Lachlanric/Robot-Arm-Snatcha/3D/SOLIDWORKS/Assem1.SLDASM

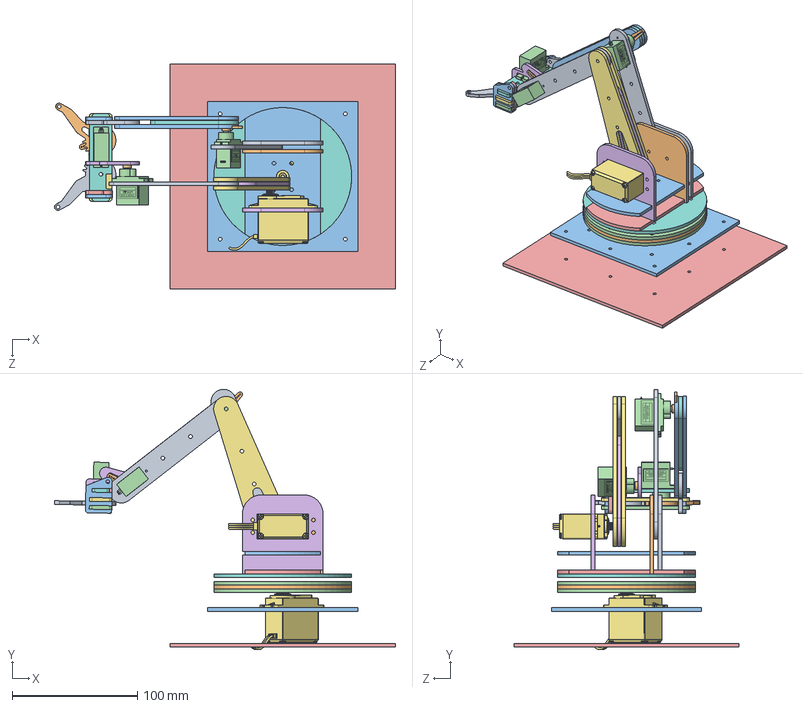
[picture p4: CAD file, 2025-02-07]
3D/SOLIDWORKS/Assem1.SLDASM
272.2 x 207.8 x 180.0 mm
M90S x 3
L1_body x 2
MG90S_horn1 x 3
L1_body - motor mount x 2
L1_body - middle spacing
MG995_large x 2
BaseMotorSlot
BaseHorizontalSlots
CircleBase-InnerBottom
BaseSquare
CircleBase-OuterBottom - 2
BaseMotorSlot_SingleHole
CircleBase-InnerTop - 3
L1_body_taper x 2
L1_body - middle spacing - mg995r taperred
BaseSquare - larger_2
CircleBase - UnderHorn x 2
BaseHorizontalSlots_LastInsert
BaseMotorSlot_SingleHole_LastInsert
Claw_SidePanel
Claw_MotorSlot
Claw_GearSlot
Claw_SidePanel_Short
Claw_SidePanel_Shorter
Claw_Bottom_2
Claw_SidePanel_Shorter - Lock x 2
Gear1
Gear2
