Lachlanric/Robot-Arm-Snatcha/3D/SOLIDWORKS/Claw_SidePanel_Shorter - Lock.SLDPRT

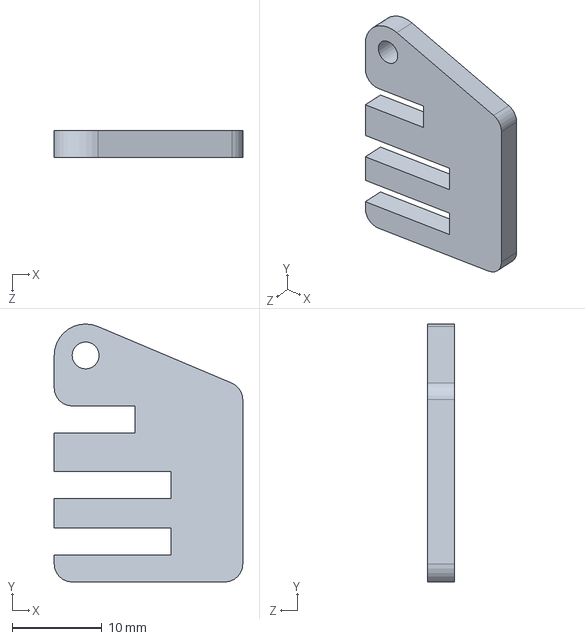
[picture p19: CAD file, 2025-02-05]
3D/SOLIDWORKS/Claw_SidePanel_Shorter - Lock.SLDPRT
21.0 x 28.7 x 3.00 mm
