Lachlanric/Robot-Arm-Snatcha/3D/SOLIDWORKS/BaseSquare - larger_2.SLDPRT

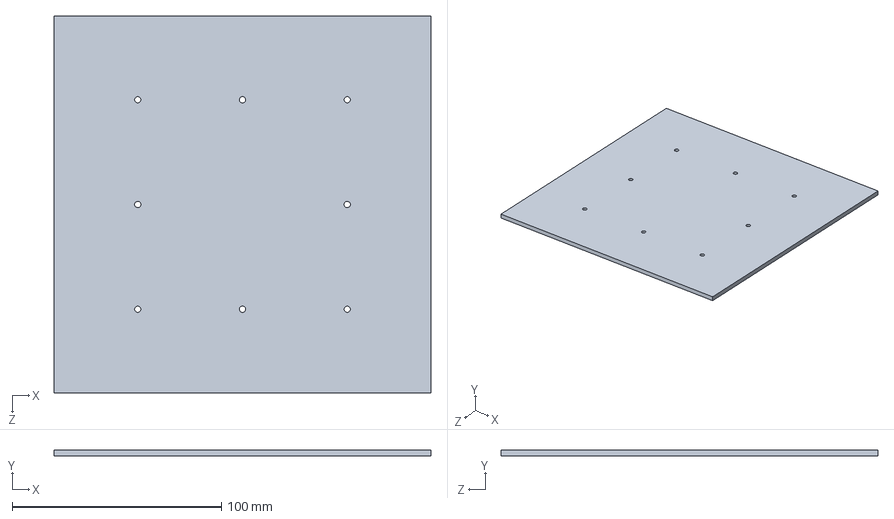
[picture p20: CAD file, 2025-02-05]
3D/SOLIDWORKS/BaseSquare - larger_2.SLDPRT
180.0 x 3.00 x 180.0 mm
