Lachlanric/Robot-Arm-Snatcha/3D/SOLIDWORKS/L1_body_taper.SLDPRT

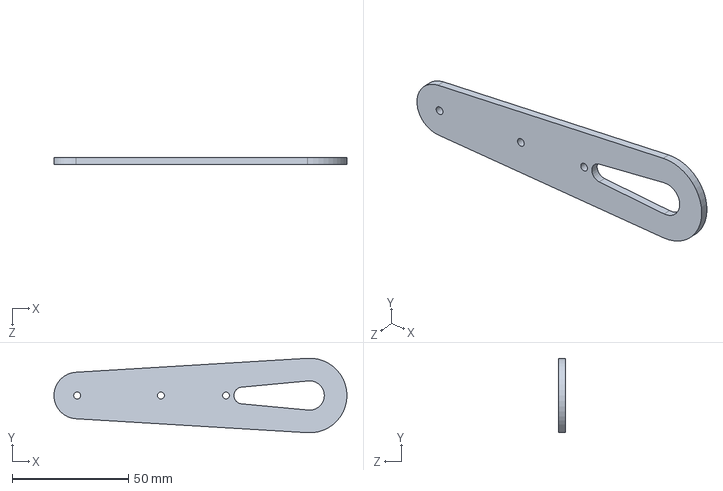
[picture p21: CAD file, 2025-02-05]
3D/SOLIDWORKS/L1_body_taper.SLDPRT
126.0 x 32.0 x 3.00 mm
