Lachlanric/Robot-Arm-Snatcha/3D/SOLIDWORKS/CircleBase-InnerTop - 3.SLDPRT

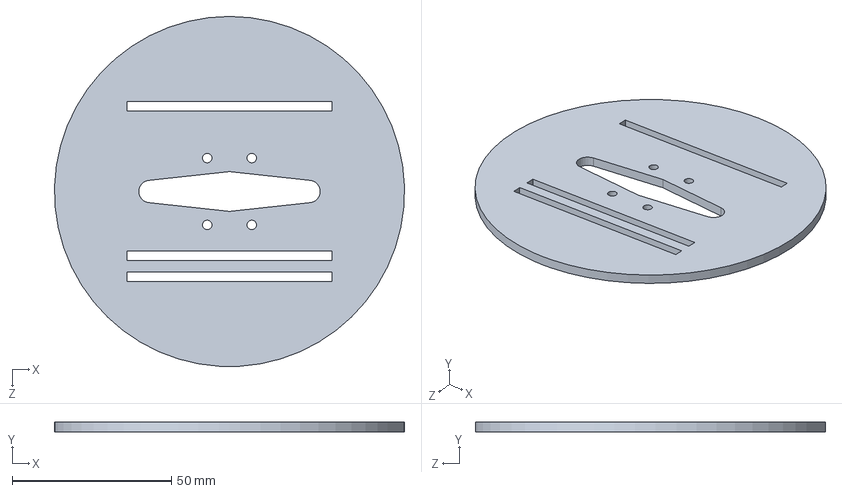
[picture p22: CAD file, 2025-02-05]
3D/SOLIDWORKS/CircleBase-InnerTop - 3.SLDPRT
110.0 x 3.00 x 110.0 mm
