Lachlanric/Robot-Arm-Snatcha/3D/SOLIDWORKS/MG995_large.SLDPRT

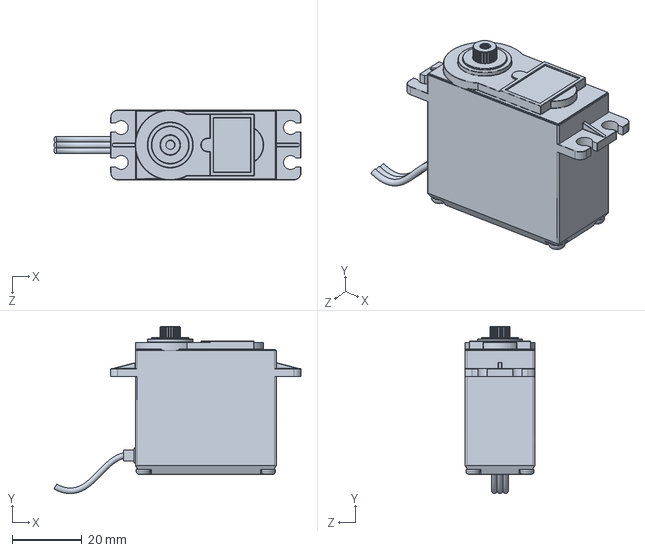
[picture p23: CAD file, 2025-02-05]
3D/SOLIDWORKS/MG995_large.SLDPRT
70.7 x 47.9 x 20.0 mm
