Lachlanric/Robot-Arm-Snatcha/3D/SOLIDWORKS/BaseHorizontalSlots_LastInsert.SLDPRT

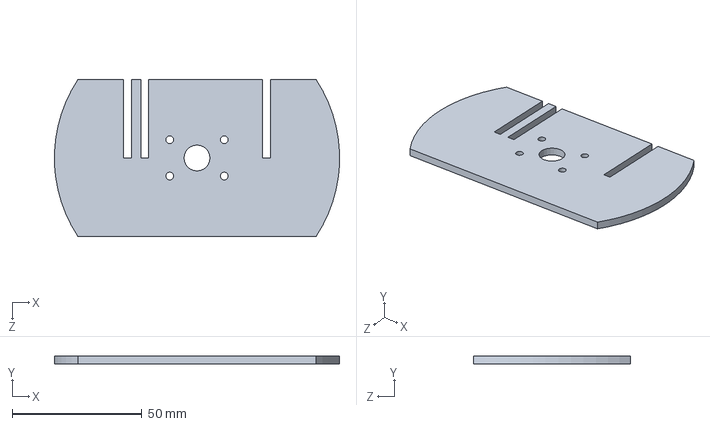
[picture p24: CAD file, 2025-02-05]
3D/SOLIDWORKS/BaseHorizontalSlots_LastInsert.SLDPRT
109.9 x 3.00 x 60.5 mm
