Lachlanric/Robot-Arm-Snatcha/3D/SOLIDWORKS/MG90S_horn1.SLDPRT

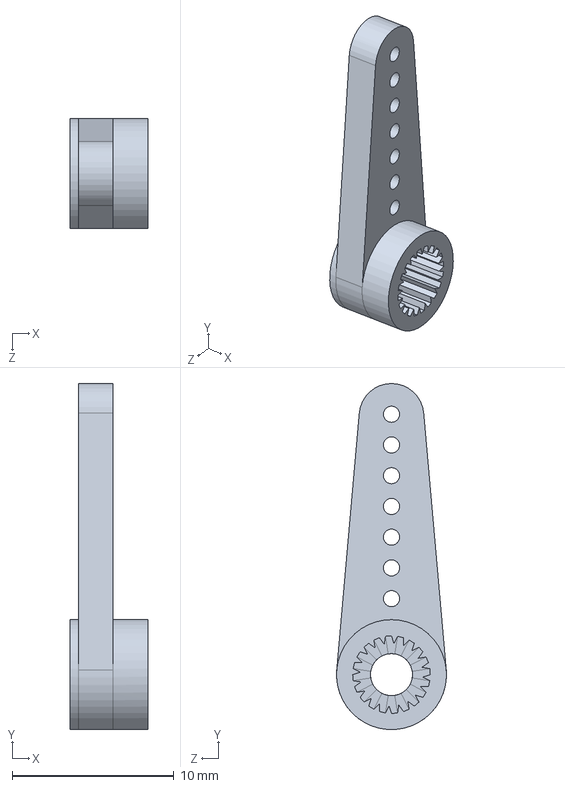
[picture p25: CAD file, 2025-02-05]
3D/SOLIDWORKS/MG90S_horn1.SLDPRT
4.80 x 21.4 x 6.80 mm
