Lachlanric/Robot-Arm-Snatcha/3D/SOLIDWORKS/M90S.SLDPRT

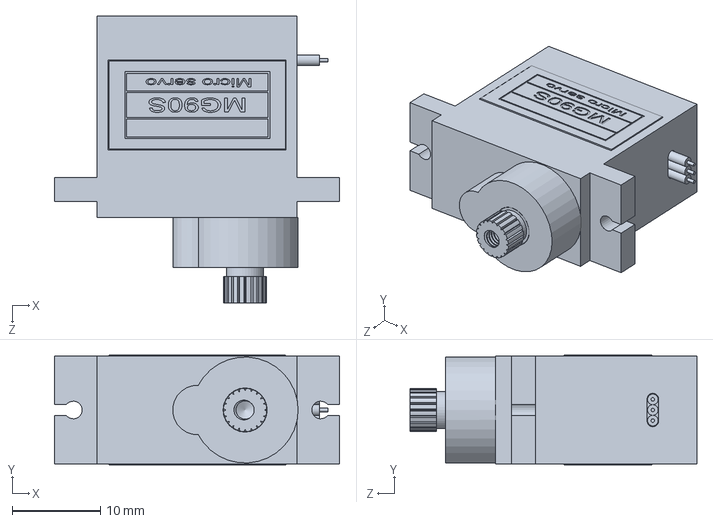
[picture p27: CAD file, 2025-02-05]
3D/SOLIDWORKS/M90S.SLDPRT
32.3 x 12.4 x 32.5 mm
