Lachlanric/Robot-Arm-Snatcha/3D/SOLIDWORKS/BaseMotorSlot_SingleHole_LastInsert.SLDPRT

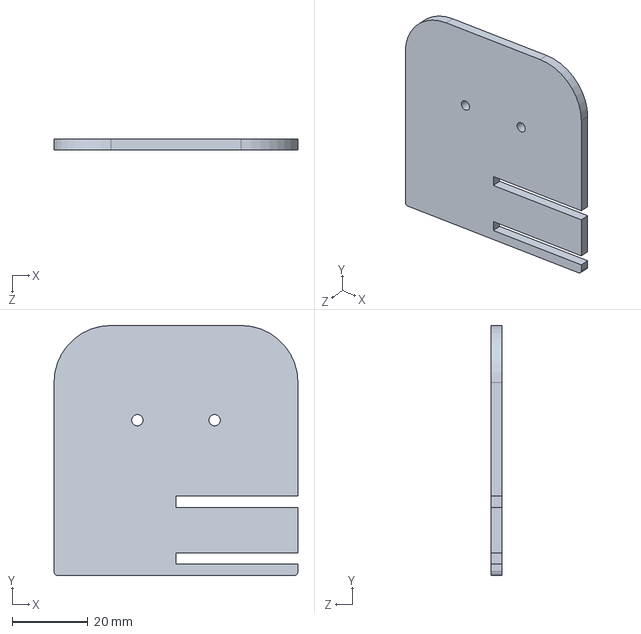
[picture p28: CAD file, 2025-02-05]
3D/SOLIDWORKS/BaseMotorSlot_SingleHole_LastInsert.SLDPRT
64.4 x 66.0 x 3.00 mm
