Lachlanric/Robot-Arm-Snatcha/3D/SOLIDWORKS/L1_body - middle spacing - mg995r taperred.SLDPRT

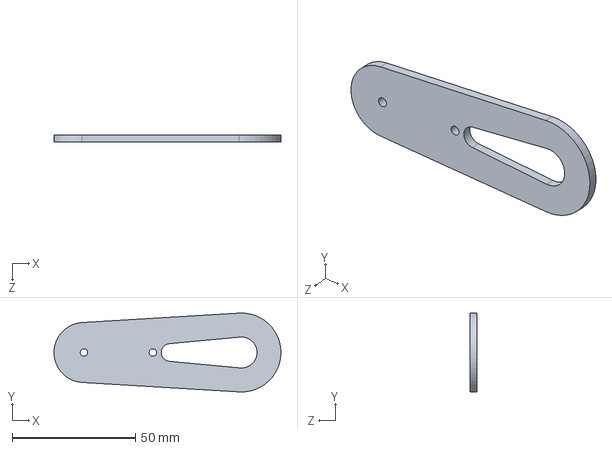
[picture p29: CAD file, 2025-02-05]
3D/SOLIDWORKS/L1_body - middle spacing - mg995r taperred.SLDPRT
92.2 x 32.0 x 3.00 mm
