Lachlanric/Robot-Arm-Snatcha/3D/SOLIDWORKS/L1_body - middle spacing.SLDPRT

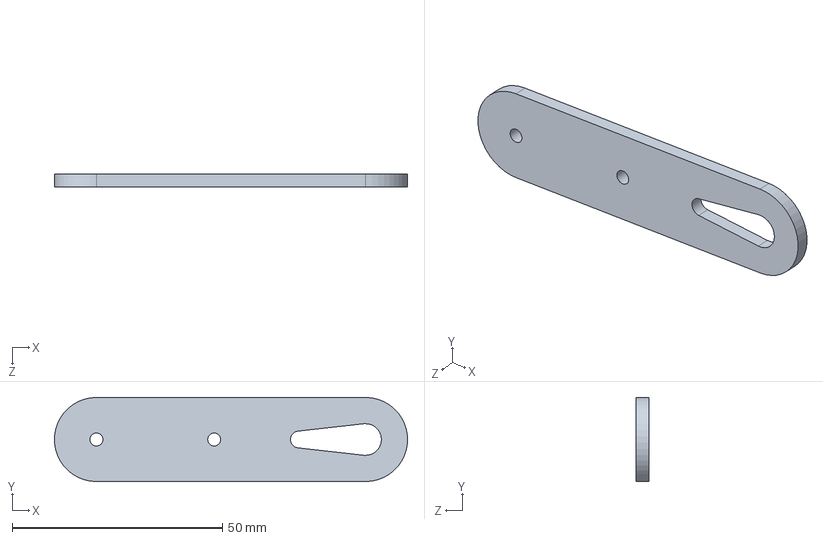
[picture p30: CAD file, 2025-02-05]
3D/SOLIDWORKS/L1_body - middle spacing.SLDPRT
83.9 x 20.0 x 3.00 mm
