Lachlanric/Robot-Arm-Snatcha/3D/SOLIDWORKS/Gear2.SLDPRT

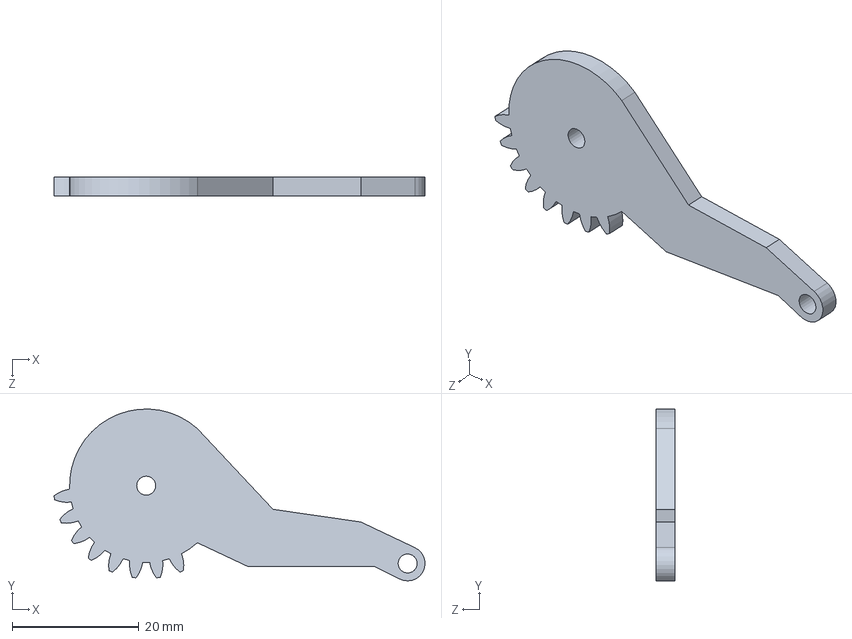
[picture p31: CAD file, 2025-02-05]
3D/SOLIDWORKS/Gear2.SLDPRT
58.5 x 27.1 x 3.00 mm
